profdc9/PowerAmpAudio/Docs/Grounding.pdf

# Basic Power and Grounding Scheme for Amplifier

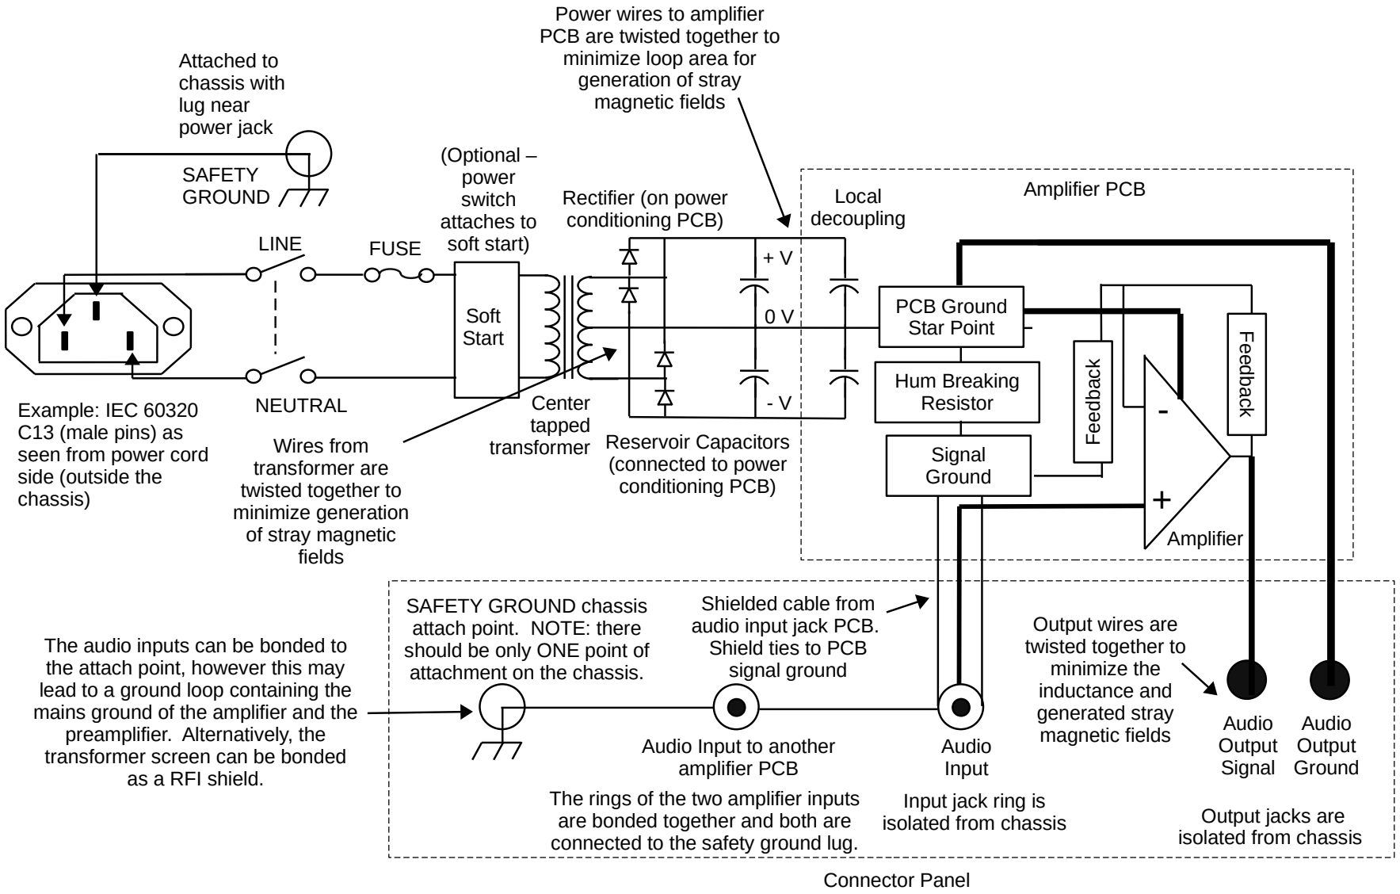
[picture p3: figure]
LINE; NEUTRAL; SAFETY GROUND; Example: IEC 60320 C13 (male pins) as seen from power cord side (outside the chassis); FUSE; Center tapped transformer; Rectifier (on power conditioning PCB); Attached to chassis with lug near power jack; Reservoir Capacitors (connected to power conditioning PCB); Local decoupling; Connector Panel; PCB Ground Star Point; Audio Input; Input jack ring is isolated from chassis; Shielded cable from audio input jack PCB. Shield ties to PCB signal ground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
