profdc9/PowerAmpAudio/PowerampC300TO126/Poweramp-Schematic.pdf

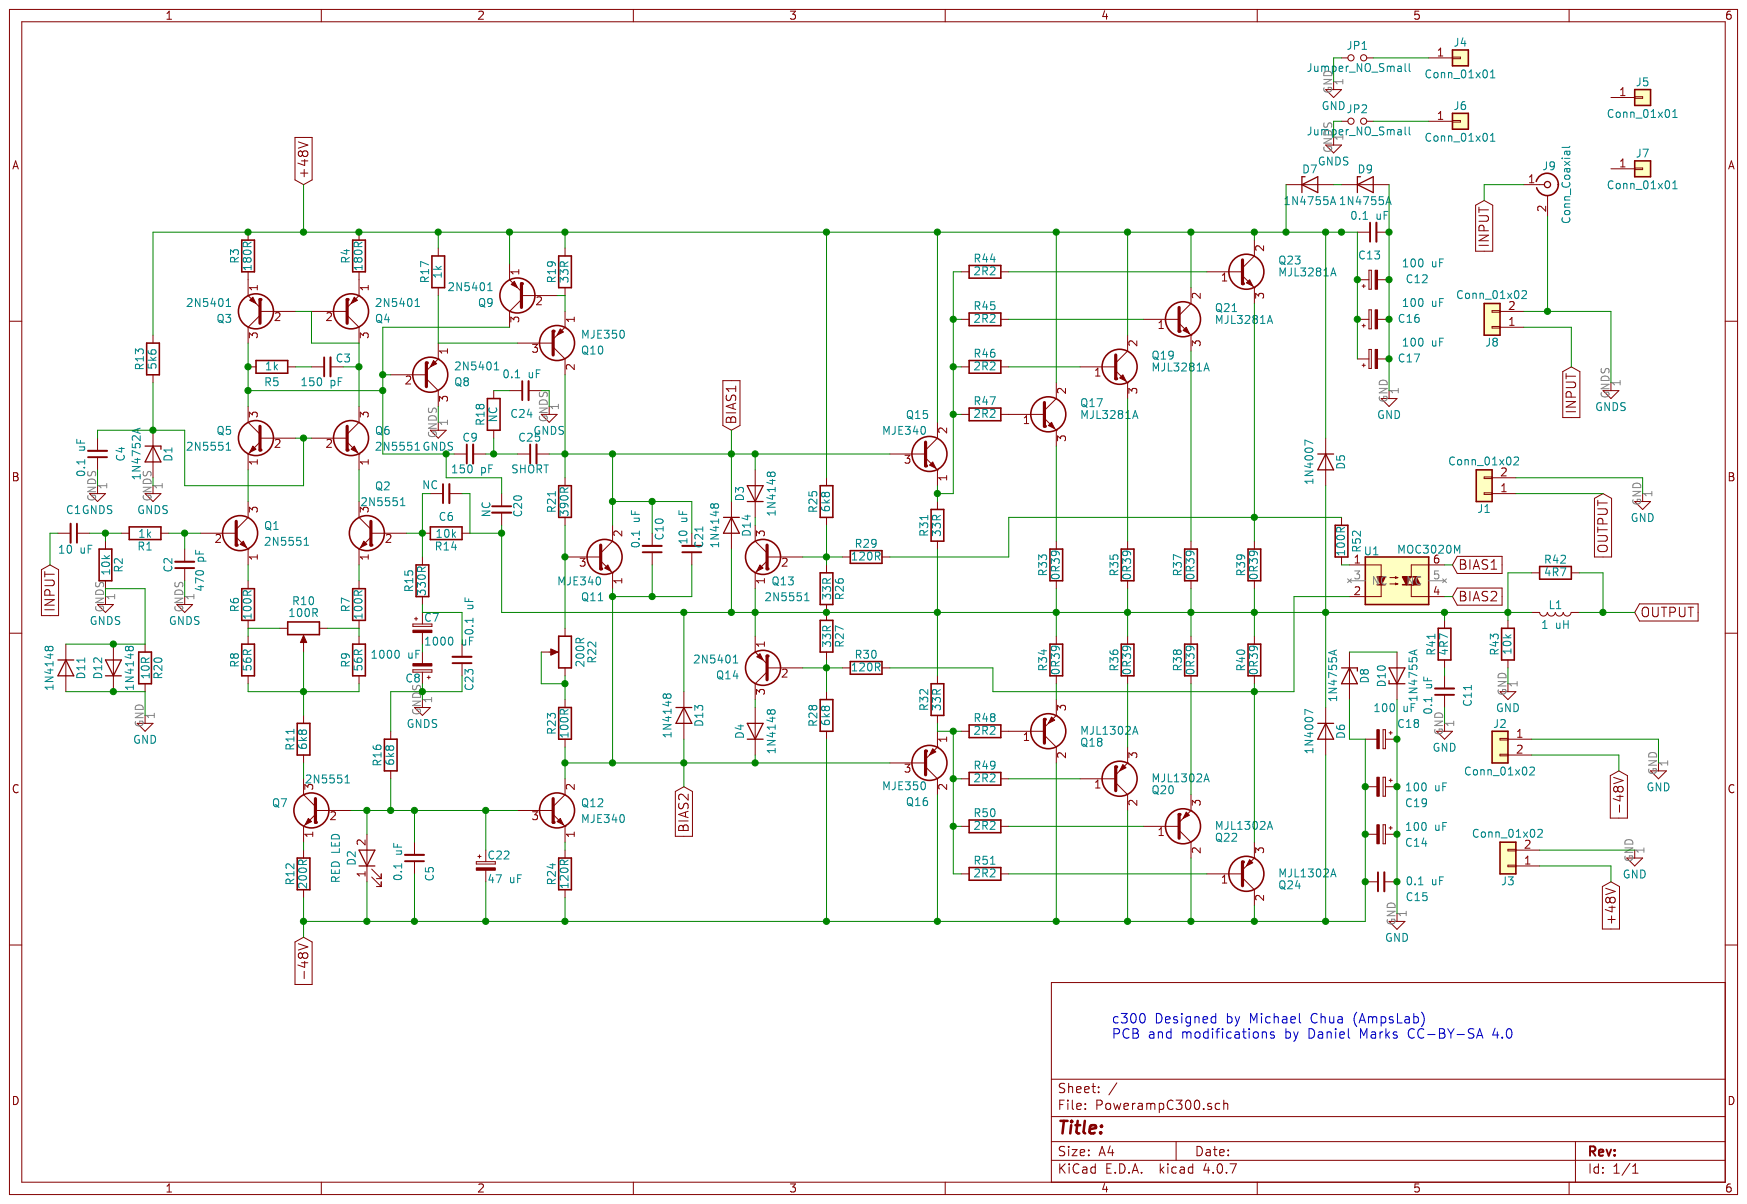
[picture p23: page 1]
